mail2adnanyazik-bit/Splitboard/assets/img/2026-06-29-20-37-37.png

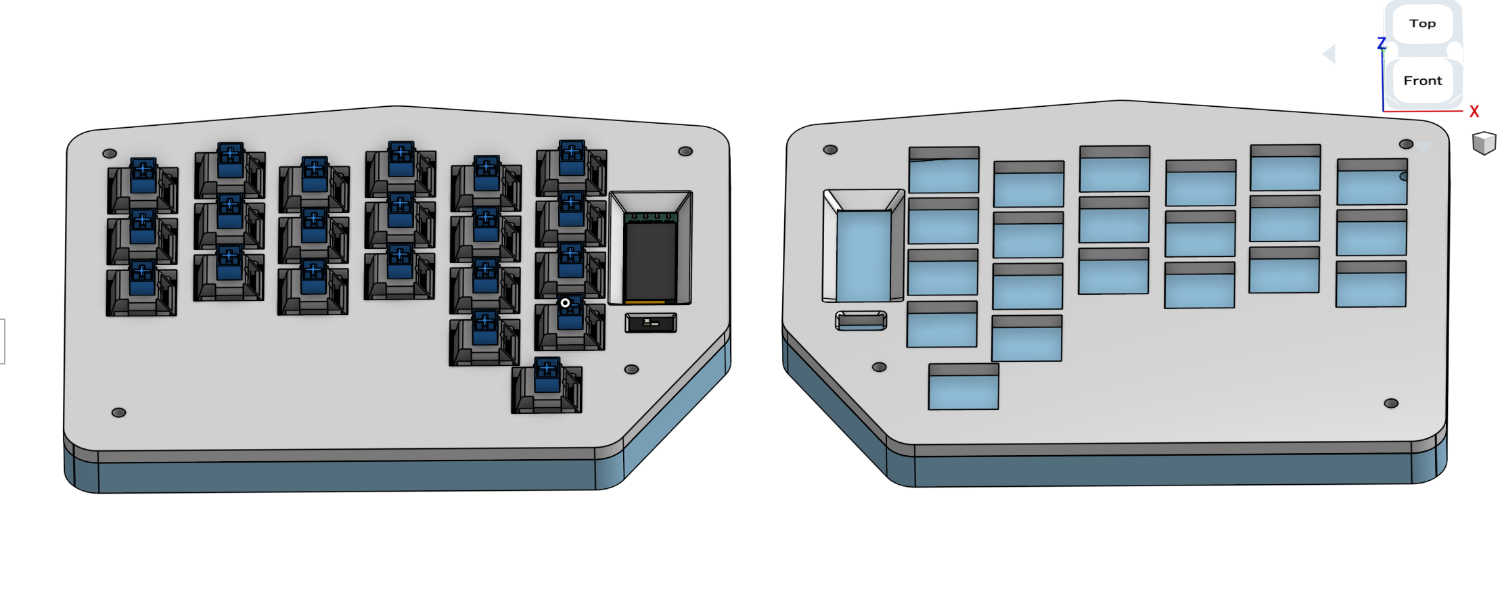
assets/img/2026-06-29-20-37-37.png
