mail2adnanyazik-bit/Splitboard/assets/img/2026-06-29-20-59-36.png

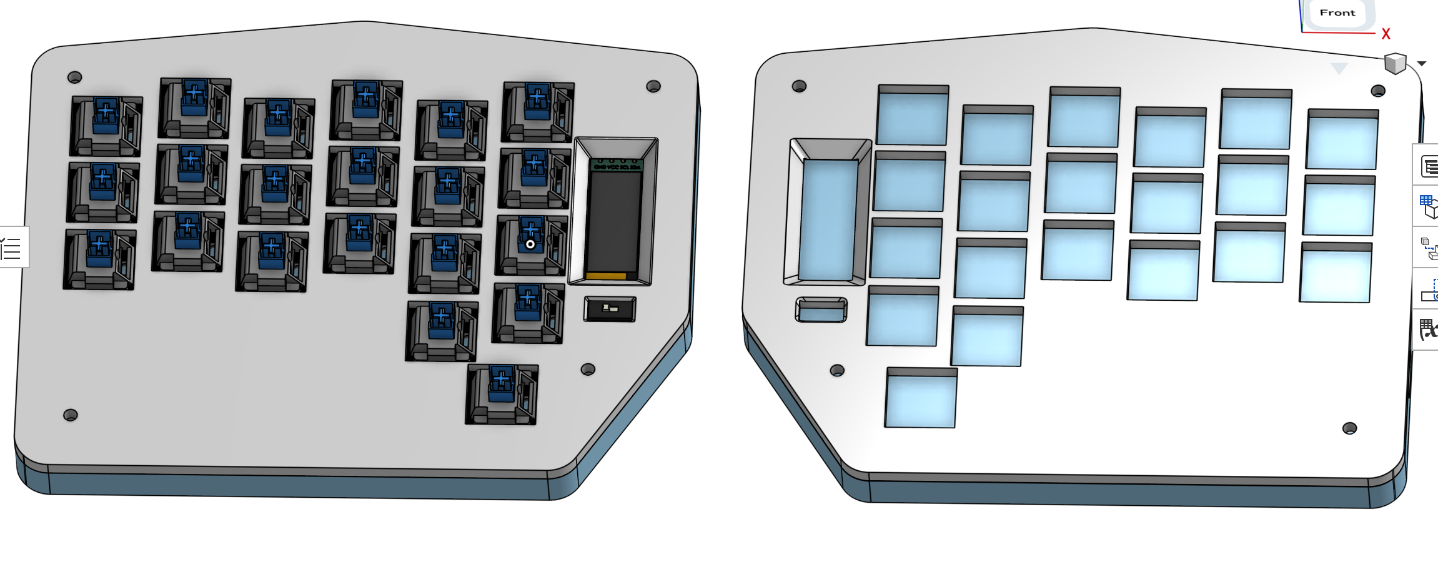
assets/img/2026-06-29-20-59-36.png
